Illinois-tech-ITM/BSMP-2016-Door-Opening-Warning-Sensor/Documents/Case Fabrication_1.jpg

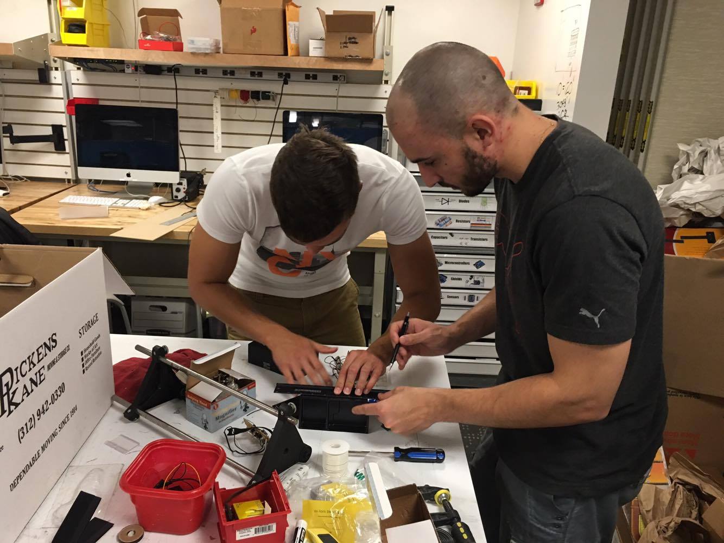
Documents/Case Fabrication_1.jpg
